heyspacebuck/kicad_goose/code/arduino_honk/gooseaudio.h

#ifndef GOOSEAUDIO_H
#define GOOSEAUDIO_HIO_H
#define DATA_LENGTH 3021
const PROGMEM unsigned char audio[DATA_LENGTH] = { 0x80, 0x80, 0x80, 0x7f, 0x7f, 0x7f, 0x7f, 0x7f, 0x7f, 0x7f, 0x80, 0x80, 0x81, 0x81, 0x80, 0x80, 0x80, 0x7f, 0x7f, 0x7f, 0x7f, 0x7f, 0x7f, 0x7f, 0x7f, 0x7f, 0x7f, 0x7f, 0x7f, 0x7f, 0x80, 0x80, 0x80, 0x80, 0x80, 0x80, 0x80, 0x80, 0x80, 0x7f, 0x7f, 0x7f, 0x7f, 0x7f, 0x7f, 0x7f, 0x7f, 0x80, 0x80, 0x80, 0x80, 0x80, 0x80, 0x80, 0x80, 0x80, 0x7f, 0x7f, 0x80, 0x80, 0x80, 0x7f, 0x80, 0x80, 0x7f, 0x7f, 0x7f, 0x7f, 0x7f, 0x7f, 0x7f, 0x80, 0x80, 0x80, 0x80, 0x80, 0x80, 0x80, 0x7f, 0x80, 0x80, 0x7f, 0x7f, 0x7f, 0x7f, 0x7f, 0x7f, 0x7f, 0x7f, 0x7f, 0x80, 0x80, 0x80, 0x80, 0x80, 0x7f, 0x7f, 0x7f, 0x7f, 0x7f, 0x7f, 0x7f, 0x7f, 0x7f, 0x7f, 0x7f, 0x7f, 0x7f, 0x7f, 0x7f, 0x7e, 0x7e, 0x7e, 0x7f, 0x7e, 0x7f, 0x7f, 0x7f, 0x7f, 0x7e, 0x7e, 0x7e, 0x7e, 0x7e, 0x7d, 0x7d, 0x7d, 0x7d, 0x7d, 0x7d, 0x7d, 0x7d, 0x7e, 0x7f, 0x81, 0x82, 0x83, 0x84, 0x85, 0x86, 0x85, 0x85, 0x84, 0x83, 0x82, 0x80, 0x7f, 0x7d, 0x7c, 0x7a, 0x77, 0x74, 0x6e, 0x6e, 0x6f, 0x71, 0x7a, 0x86, 0x8d, 0x90, 0x93, 0x93, 0x8e, 0x87, 0x85, 0x85, 0x87, 0x86, 0x87, 0x87, 0x85, 0x81, 0x7e, 0x7b, 0x7a, 0x7a, 0x7c, 0x7e, 0x7f, 0x7f, 0x7f, 0x7e, 0x7c, 0x7c, 0x7c, 0x7e, 0x80, 0x83, 0x85, 0x86, 0x86, 0x87, 0x86, 0x83, 0x80, 0x7d, 0x7a, 0x77, 0x77, 0x78, 0x78, 0x7a, 0x7d, 0x7e, 0x7e, 0x7e, 0x80, 0x81, 0x82, 0x82, 0x83, 0x85, 0x85, 0x86, 0x86, 0x85, 0x85, 0x84, 0x83, 0x82, 0x81, 0x7f, 0x7d, 0x7b, 0x79, 0x78, 0x78, 0x76, 0x75, 0x76, 0x76, 0x7a, 0x7c, 0x7f, 0x82, 0x80, 0x7d, 0x7f, 0x81, 0x82, 0x80, 0x7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
0, 0x80, 0x80, 0x80, 0x80, 0x80, 0x80, 0x80, 0x7f, 0x7f, 0x7e, 0x7f, 0x80, 0x7f, 0x80, 0x80, 0x7f, 0x80, 0x80, 0x80, 0x80, 0x7f, 0x80, 0x7f, 0x80, 0x80, 0x80, 0x80, 0x80, 0x80 };
#endif
